Susssiest/Custom-Keyboard/CAD/STEPS/PCB Render.step

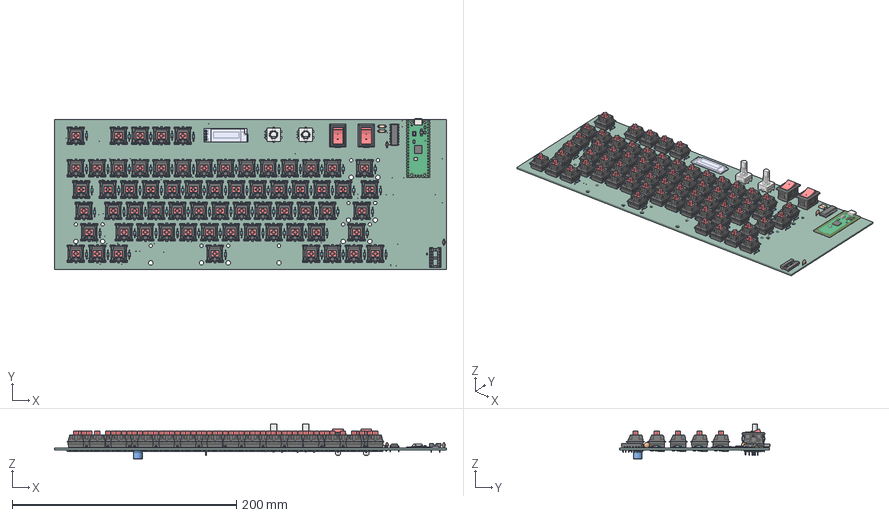
[picture p8: CAD file, 2026-09-23]
CAD/STEPS/PCB Render.step
349.3 x 134.1 x 31.1 mm
D_DO-35_SOD27_P7.62mm_Horizontal x 66
R_0603_1608Metric
R_Axial_DIN0207_L63mm_D25mm_P762mm_Horizontal x 2
0.91in OLED
C_Disc_D50mm_W25mm_P500mm x 2
DIP_14_W762mm_Socket
DIP-16_W7.62mm
Vypinac kolebkovy_KCD1-101_2pin x 2
RaspberryPi_Pico_Module_KiCad
Pin1 x 66
Pin2 x 66
Pin3 x 66
Pin4 x 66
CP_Radial_D80mm_P350mm
Custom Keyboard-unsaved-export-p9akFg_PCB
